DrCoolzic/MorpheusHypnoLight/doc/images/4_led_array.png

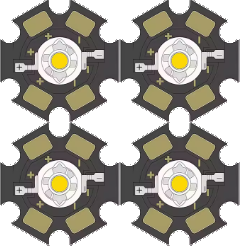
doc/images/4_led_array.png
