DrCoolzic/MorpheusHypnoLight/doc/images/5_led_array.png

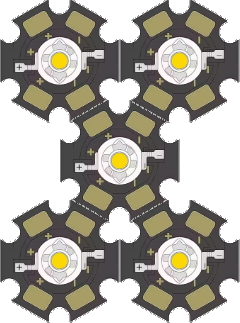
doc/images/5_led_array.png
