DrCoolzic/MorpheusHypnoLight/doc/images/6_led_array.png

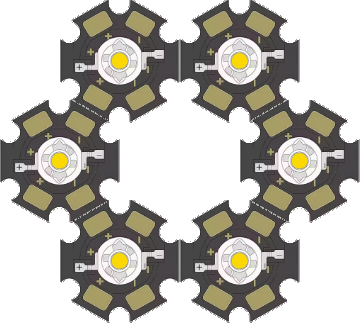
doc/images/6_led_array.png
