DrCoolzic/MorpheusHypnoLight/doc/images/ControlBoard_schem.png

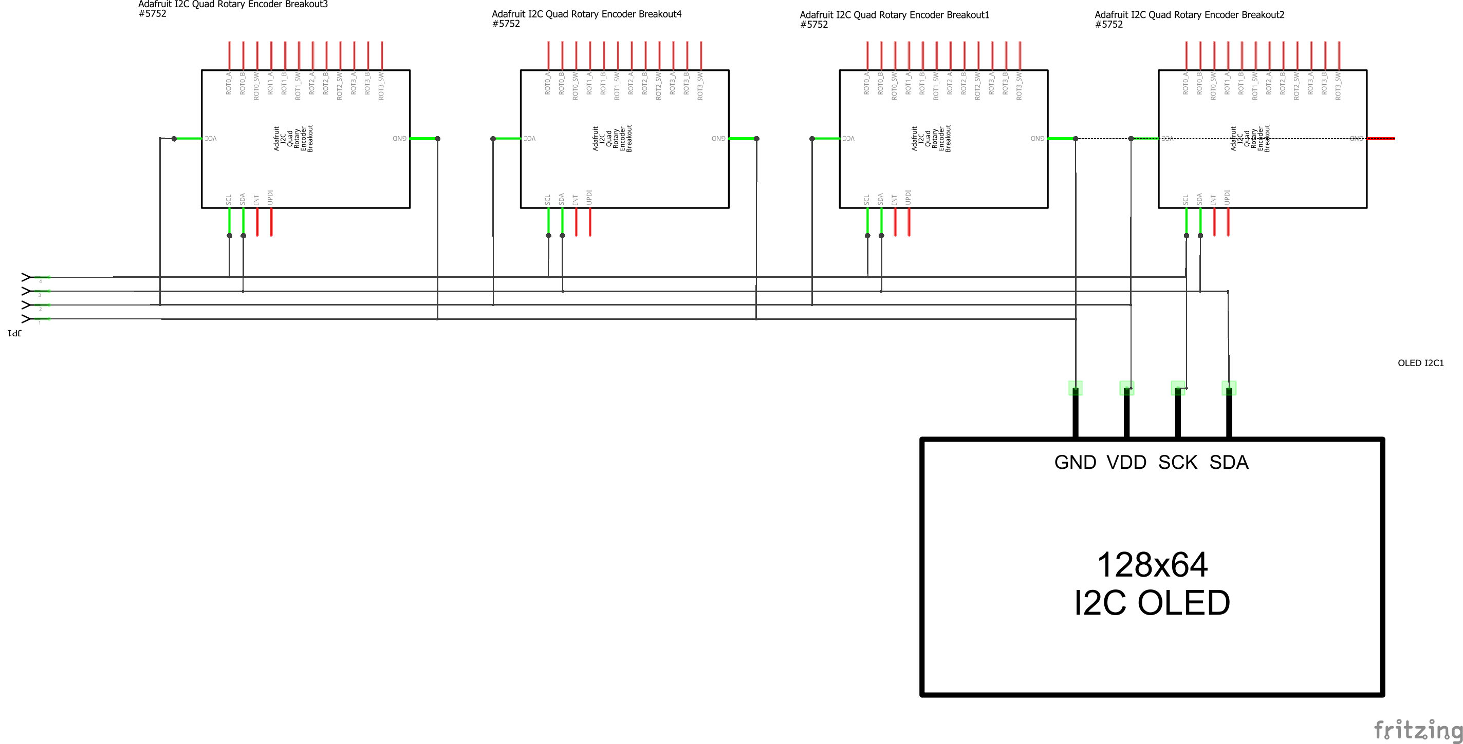
doc/images/ControlBoard_schem.png
