DrCoolzic/MorpheusHypnoLight/doc/images/EIM_03.png

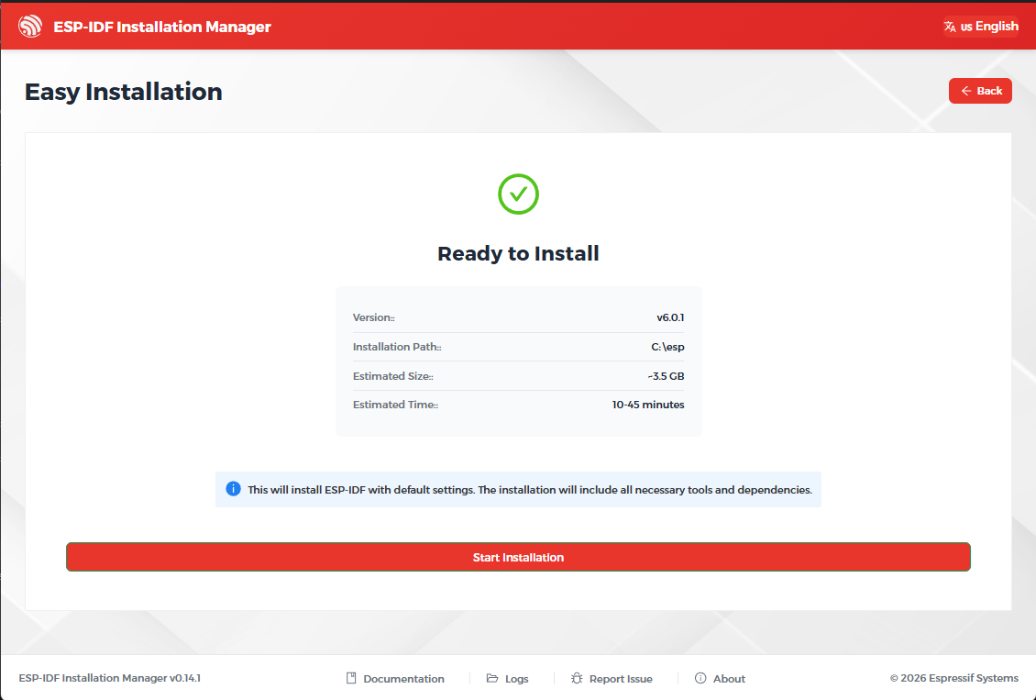
doc/images/EIM_03.png
