DrCoolzic/MorpheusHypnoLight/doc/images/pcbled.png

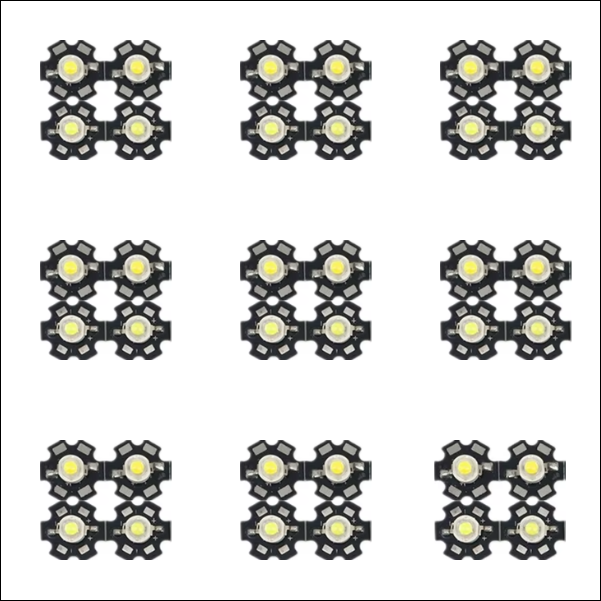
doc/images/pcbled.png
