DrCoolzic/MorpheusHypnoLight/doc/images/power_led_size.png

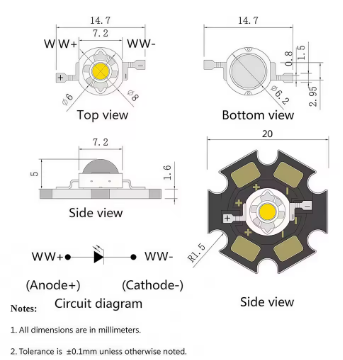
doc/images/power_led_size.png
