DrCoolzic/MorpheusHypnoLight/MorpheusHypno/MPHEditor/doc/images/image25.png

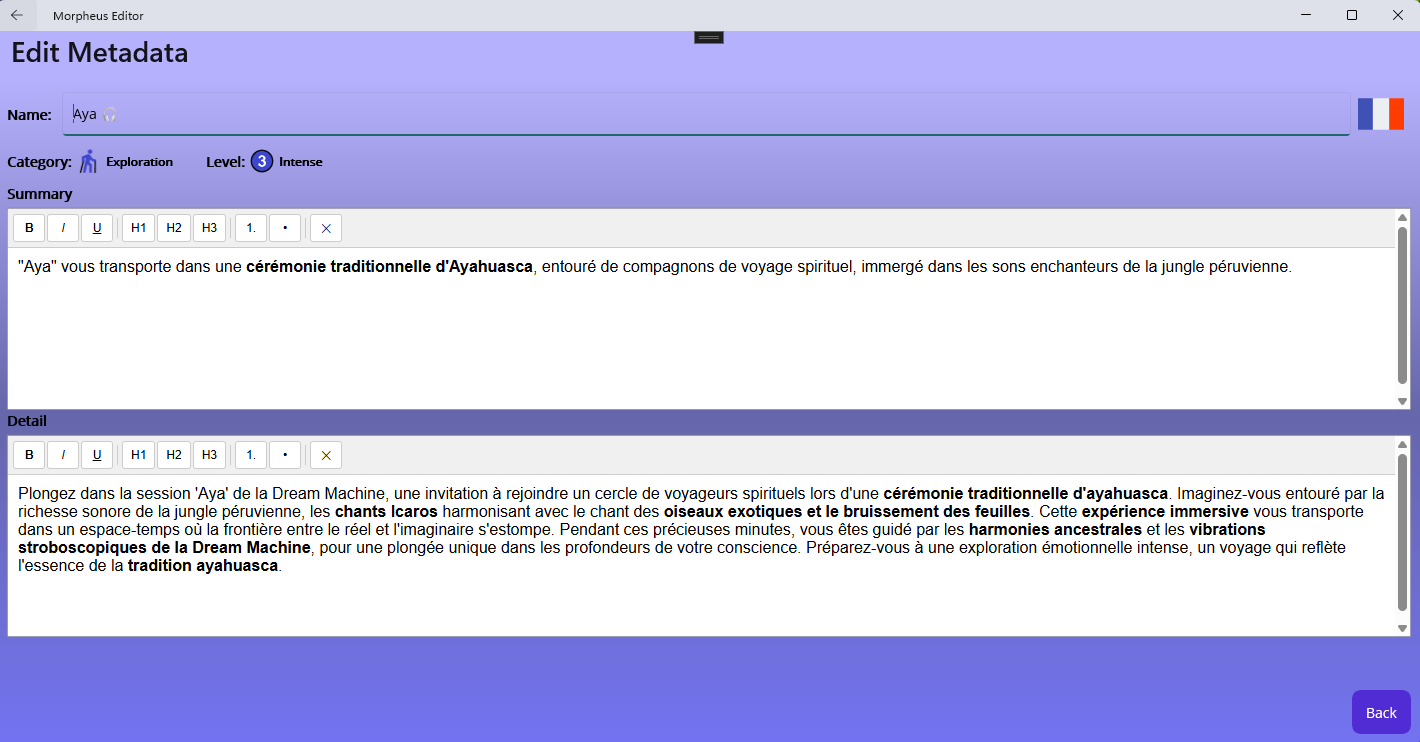
MorpheusHypno/MPHEditor/doc/images/image25.png
