DrCoolzic/MorpheusHypnoLight/MorpheusHypno/MPHEditor/Resources/Images/dmpicture.png

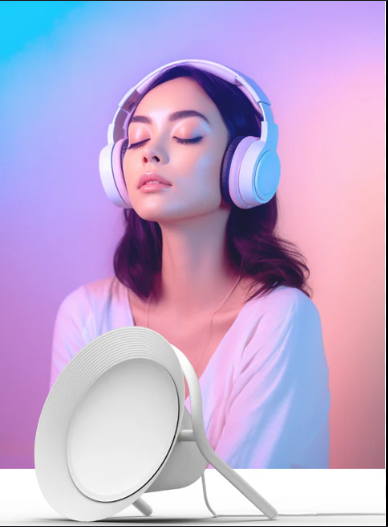
MorpheusHypno/MPHEditor/Resources/Images/dmpicture.png
