DrCoolzic/MorpheusHypnoLight/MorpheusHypno/MPHEditor/Resources/Images/gamepad_off.png

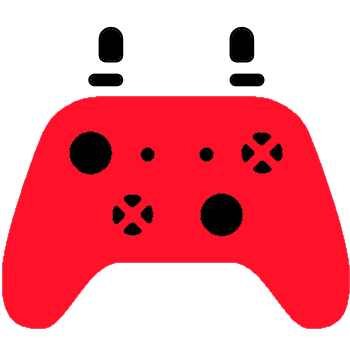
MorpheusHypno/MPHEditor/Resources/Images/gamepad_off.png
