DrCoolzic/MorpheusHypnoLight/MorpheusHypno/MPHEditor/Resources/Images/nosound.png

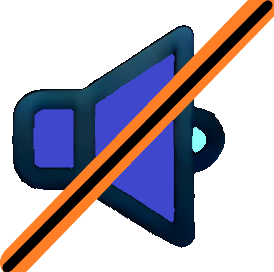
MorpheusHypno/MPHEditor/Resources/Images/nosound.png
