DrCoolzic/MorpheusHypnoLight/MorpheusHypno/MPHEditor/Resources/Images/sound.png

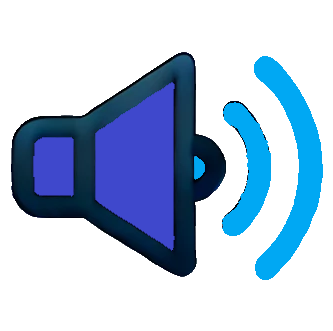
MorpheusHypno/MPHEditor/Resources/Images/sound.png
