DrCoolzic/MorpheusHypnoLight/MorpheusHypno/MPHEditor/Resources/Images/star.png

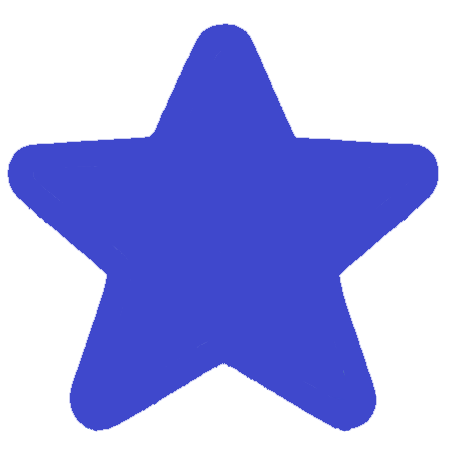
MorpheusHypno/MPHEditor/Resources/Images/star.png
