DrCoolzic/MorpheusHypnoLight/firmware/main/test_sequence_compact_data.h

#pragma once

#include <stddef.h>
#include <stdint.h>

static const uint8_t demo_sequence_compact[] = {
  0x4D, 0x48, 0x4C, 0x53, 0x01, 0x00, 0x00, 0x04, 0xF2, 0x00, 0xC0, 0x84,
  0x85, 0x46, 0x32, 0x00, 0x01, 0x00, 0x00, 0x64, 0x00, 0x00, 0x32, 0x00,
  0x32, 0x01, 0x10, 0x00, 0x64, 0x00, 0x00, 0x32, 0x00, 0x32, 0x01, 0x1F,
  0x00, 0x64, 0x00, 0x00, 0x32, 0x00, 0x32, 0x01, 0x2F, 0x00, 0x64, 0x00,
  0x00, 0x32, 0x00, 0x32, 0x00, 0x00, 0x00, 0x00, 0x00, 0x01, 0x00, 0x32,
  0x00, 0x32, 0x32, 0x00, 0x00, 0x00, 0x00, 0x96, 0x00, 0x01, 0x3C, 0x1E,
  0x00, 0x32, 0x00, 0x00, 0x00, 0x8C, 0x00, 0x01, 0x3C, 0x1E, 0x00, 0x32,
  0x00, 0x00, 0x00, 0x82, 0x00, 0x01, 0x3C, 0x1E, 0x00, 0x32, 0x00, 0x00,
  0x00, 0x78, 0x00, 0x01, 0x3C, 0x1E, 0x00, 0x32, 0x01, 0x00, 0x00, 0x0F,
  0x00, 0x01, 0x64, 0x32, 0x00, 0x32, 0x32, 0x00, 0x02, 0x00, 0x02, 0x00,
  0x05, 0x00, 0x3C, 0x00, 0x5A, 0x00, 0x00, 0x32, 0x00, 0x00, 0x02, 0x10,
  0x02, 0x00, 0x06, 0x00, 0x41, 0x00, 0x5F, 0x00, 0x00, 0x32, 0x00, 0x00,
  0x02, 0x1F, 0x02, 0x00, 0x07, 0x00, 0x46, 0x00, 0x64, 0x00, 0x00, 0x32,
  0x00, 0x00, 0x02, 0x2F, 0x02, 0x00, 0x08, 0x00, 0x4B, 0x00, 0x69, 0x00,
  0x00, 0x32, 0x00, 0x00, 0x01, 0x00, 0x00, 0x05, 0x00, 0x02, 0x00, 0x05,
  0x00, 0x1E, 0x50, 0x00, 0x32, 0x32, 0x00, 0x00, 0x00, 0x02, 0x01, 0x01,
  0x00, 0x3C, 0x00, 0x5A, 0x00, 0x00, 0x32, 0x00, 0x32, 0x00, 0x00, 0x02,
  0x01, 0x01, 0x00, 0x41, 0x00, 0x5F, 0x00, 0x00, 0x32, 0x00, 0x32, 0x00,
  0x1F, 0x02, 0x01, 0x01, 0x00, 0x46, 0x00, 0x64, 0x00, 0x00, 0x32, 0x00,
  0x32, 0x00, 0x1F, 0x02, 0x01, 0x01, 0x00, 0x4B, 0x00, 0x69, 0x00, 0x00,
  0x32, 0x00, 0x32, 0x01, 0x00, 0x00, 0x05, 0x00, 0x02, 0x00, 0x05, 0x00,
  0x1E, 0x50, 0x00, 0x32,
};

static const size_t demo_sequence_compact_size =
    sizeof(demo_sequence_compact);
